septentrio-gnss/mosaicG5-HAT/pictures/Eve&PPSO.png

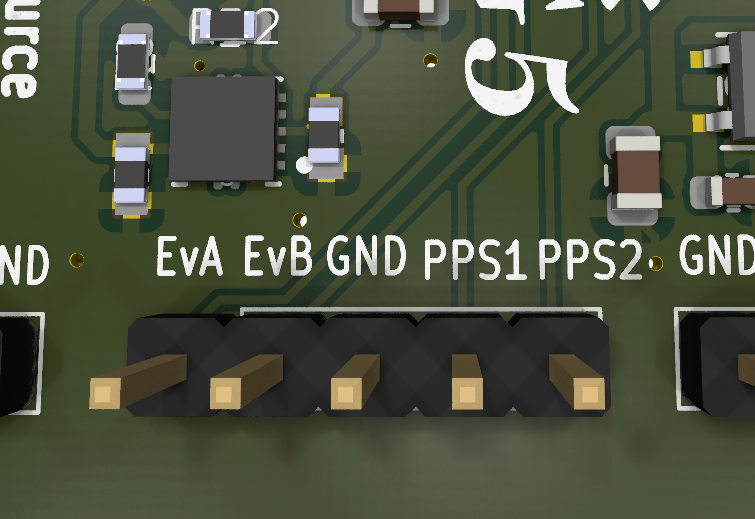
pictures/Eve&PPSO.png
