septentrio-gnss/mosaicG5-HAT/pictures/event.png

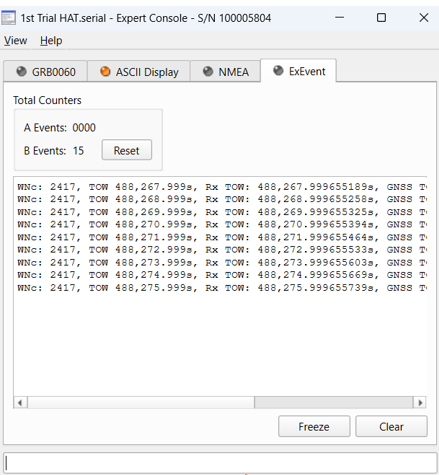
pictures/event.png
