septentrio-gnss/mosaicG5-HAT/pictures/event_console.png

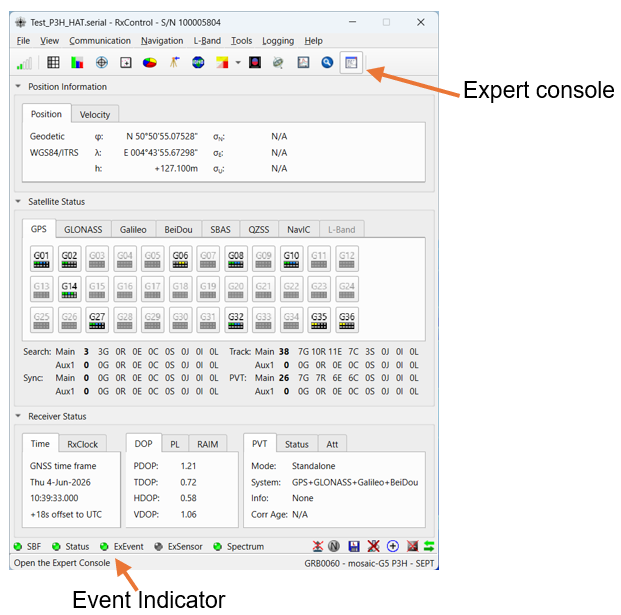
pictures/event_console.png
