septentrio-gnss/mosaicG5-HAT/pictures/FTDI_TTL.png

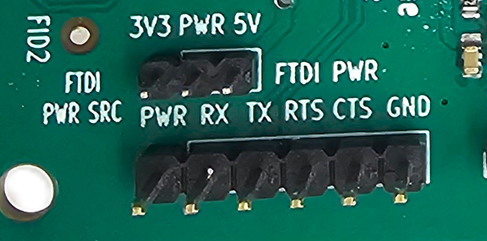
pictures/FTDI_TTL.png
