septentrio-gnss/mosaicG5-HAT/pictures/mosaicG5 h-HAT (2).jpg

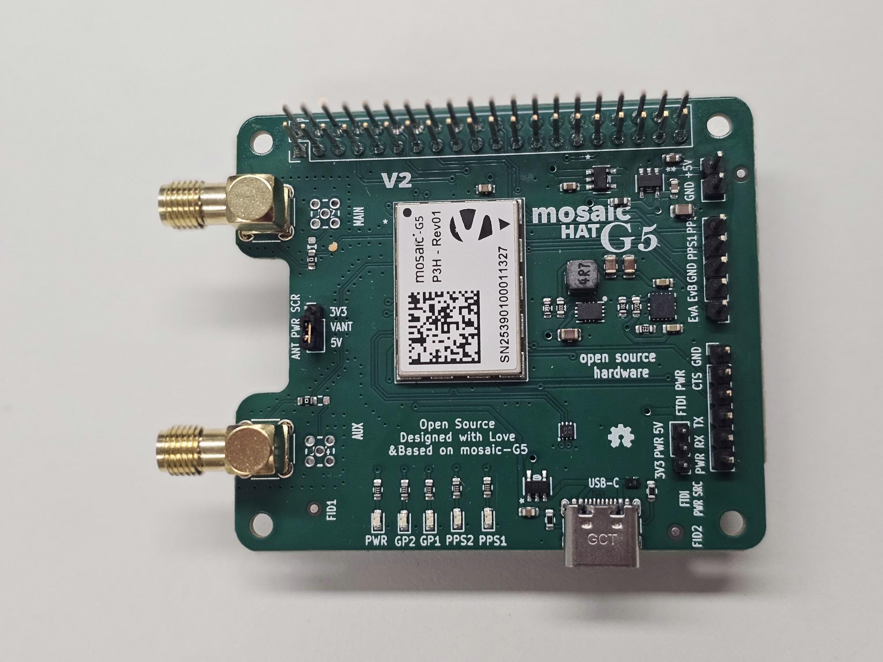
pictures/mosaicG5 h-HAT (2).jpg
