septentrio-gnss/mosaicG5-HAT/pictures/pcb.png

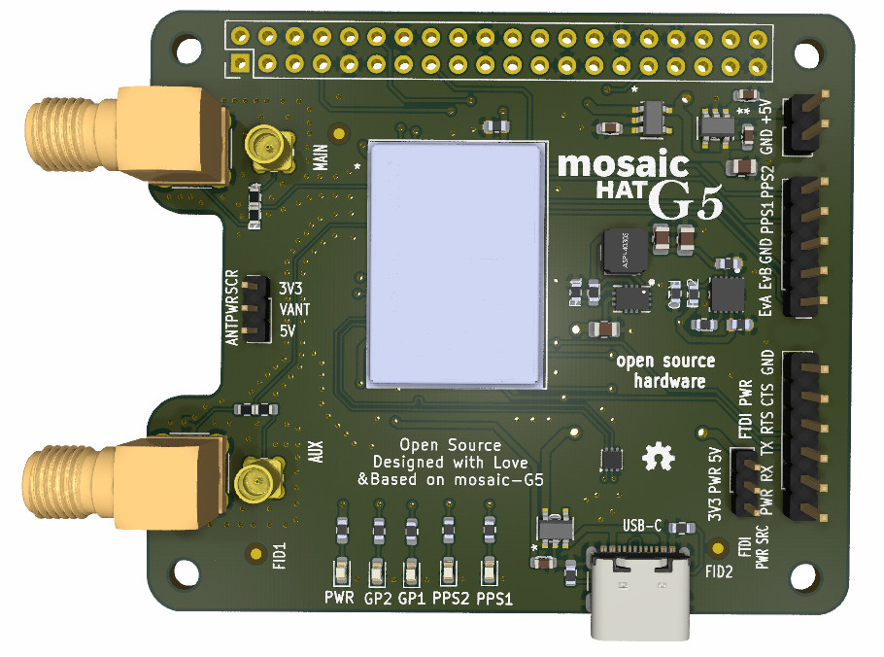
pictures/pcb.png
