septentrio-gnss/mosaicG5-HAT/pictures/PPS2_.png

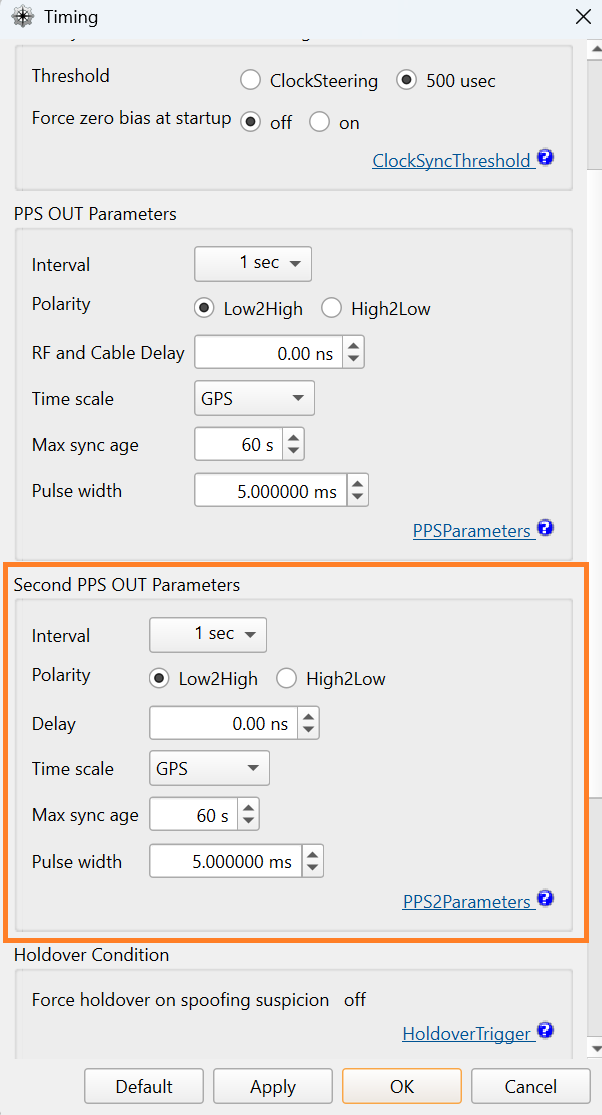
pictures/PPS2_.png
