septentrio-gnss/mosaicG5-HAT/pictures/putty.png

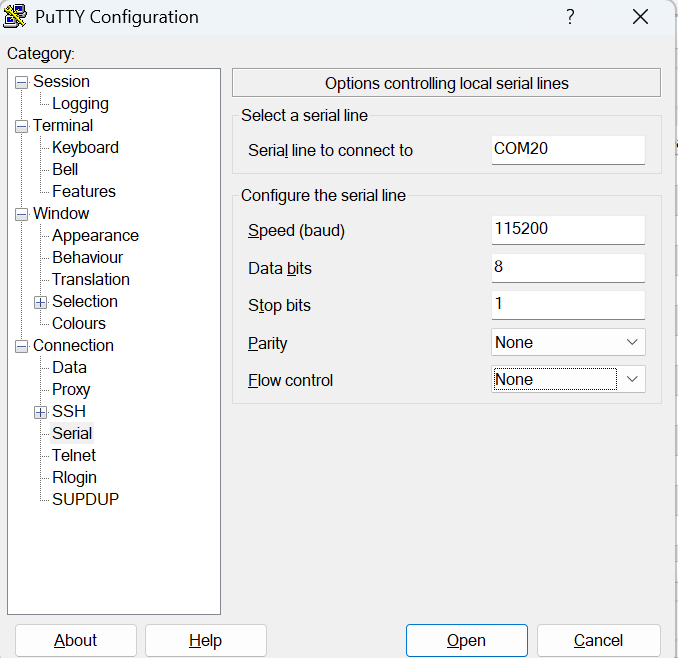
pictures/putty.png
