septentrio-gnss/mosaicG5-HAT/pictures/RPi_1.jpg

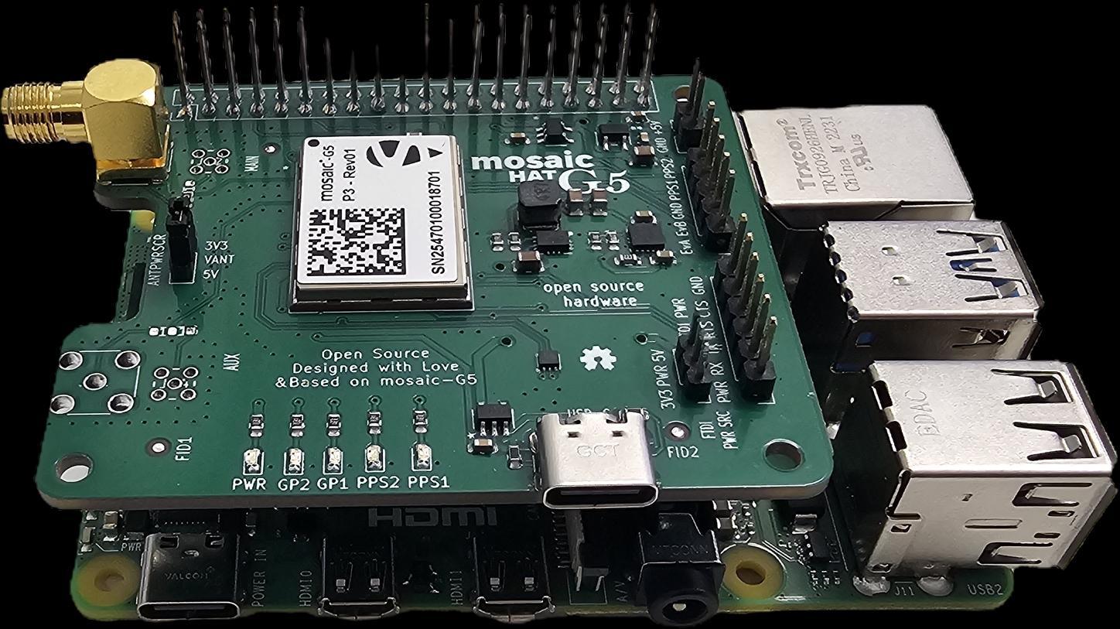
pictures/RPi_1.jpg
