septentrio-gnss/mosaicG5-HAT/pictures/rxcontrol.png

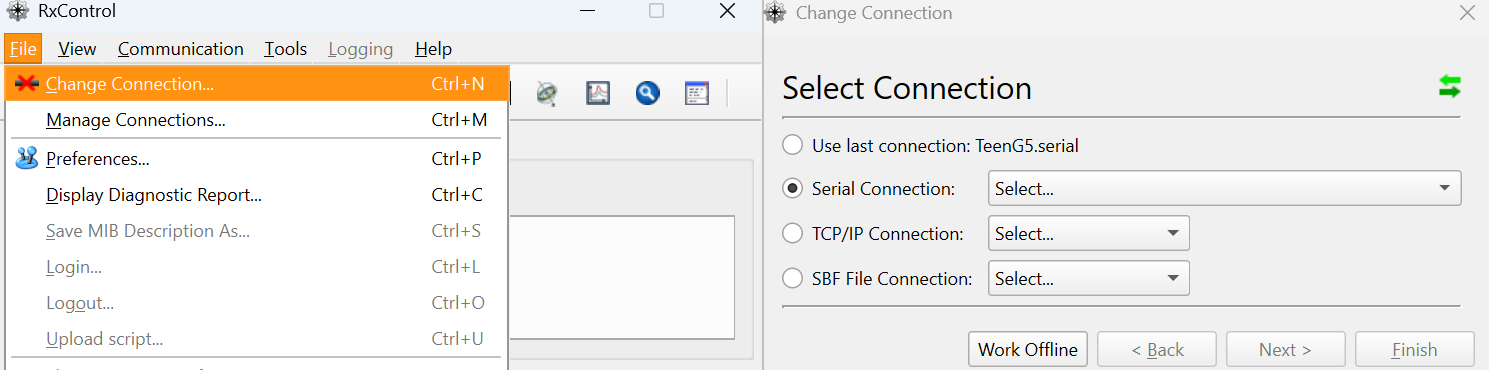
pictures/rxcontrol.png
