septentrio-gnss/mosaicG5-HAT/pictures/TLL_connection.png

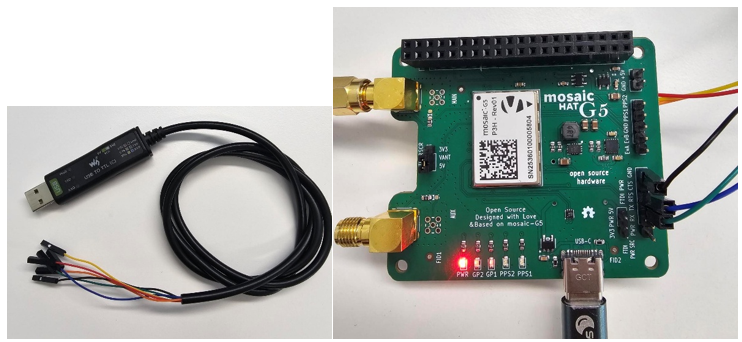
pictures/TLL_connection.png
