septentrio-gnss/mosaicG5-HAT/pictures/TTL.jpg

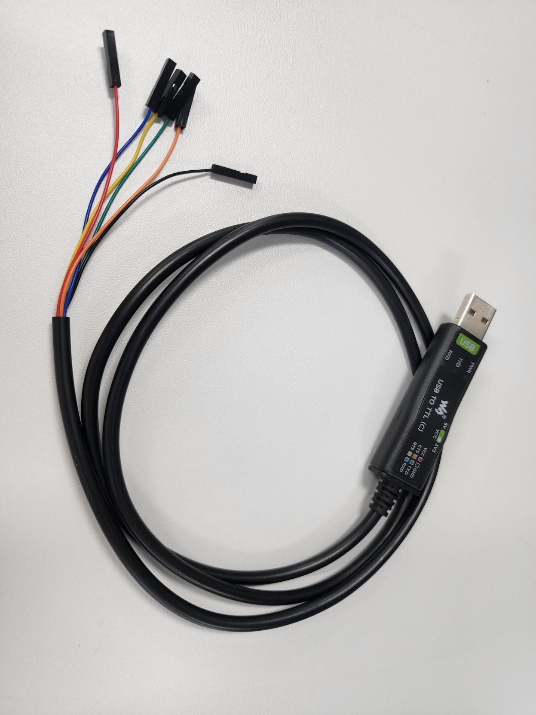
pictures/TTL.jpg
